jtryon/openclack/prototype_images/pcb_mounted.jpg

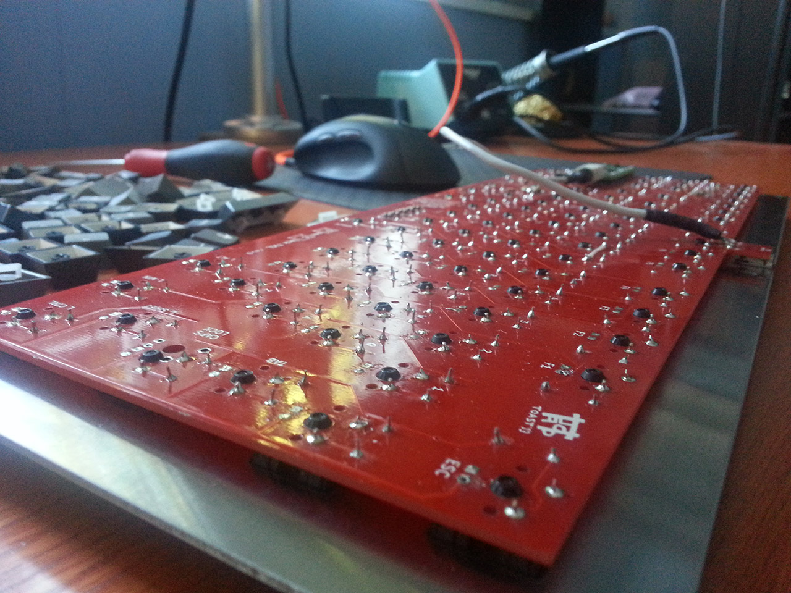
prototype_images/pcb_mounted.jpg
