jtryon/openclack/prototype_images/teensy0.JPG

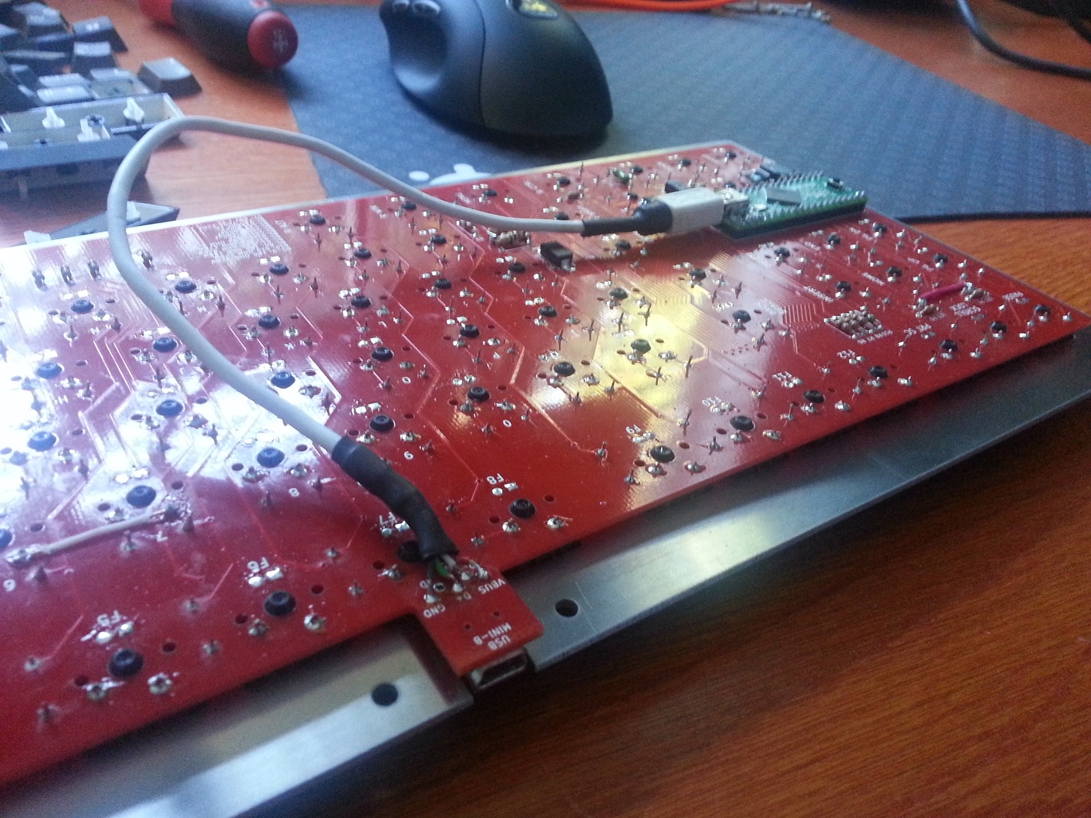
prototype_images/teensy0.JPG
